carl1961/WirelessWeatherReWork/Pictures/20250413_174417.jpg

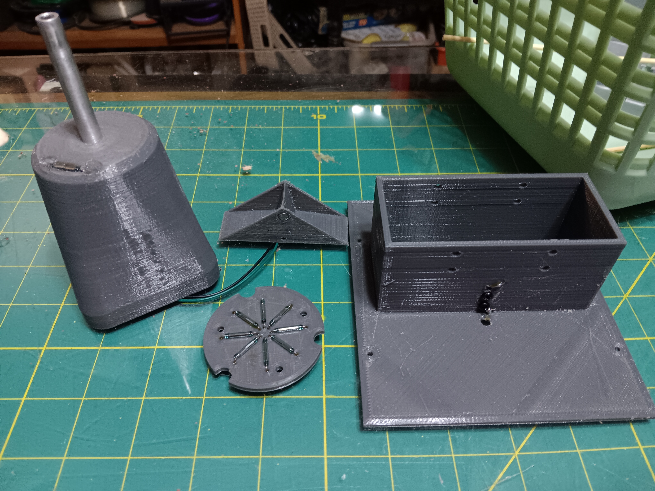
Pictures/20250413_174417.jpg
