carl1961/WirelessWeatherReWork/Pictures/20250413_174422.jpg

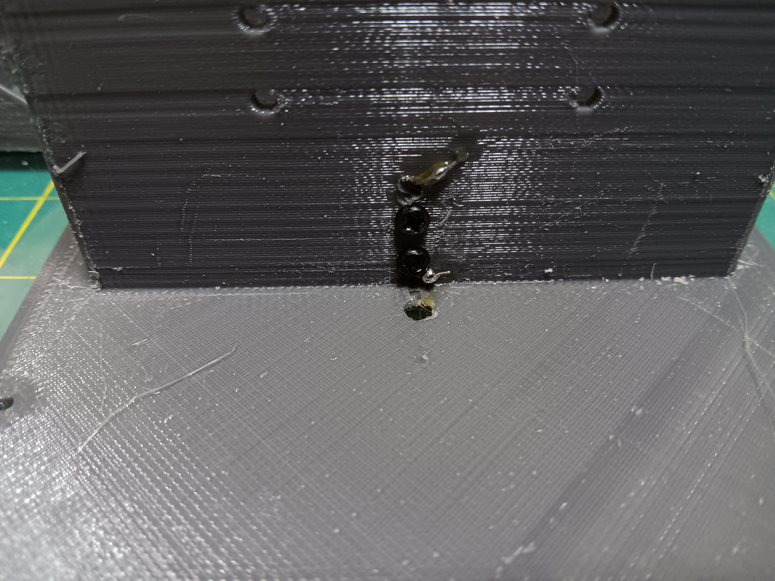
Pictures/20250413_174422.jpg
