carl1961/WirelessWeatherReWork/Pictures/20250413_174429.jpg

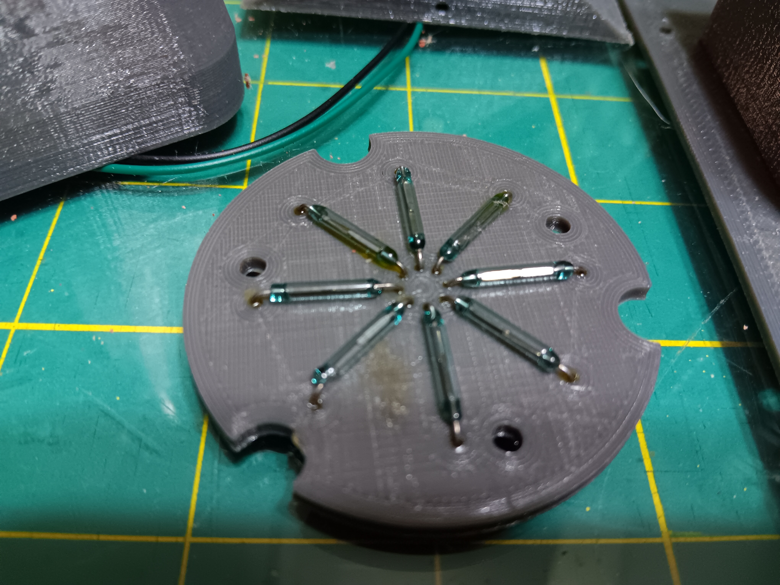
Pictures/20250413_174429.jpg
