carl1961/WirelessWeatherReWork/Pictures/20250413_174439.jpg

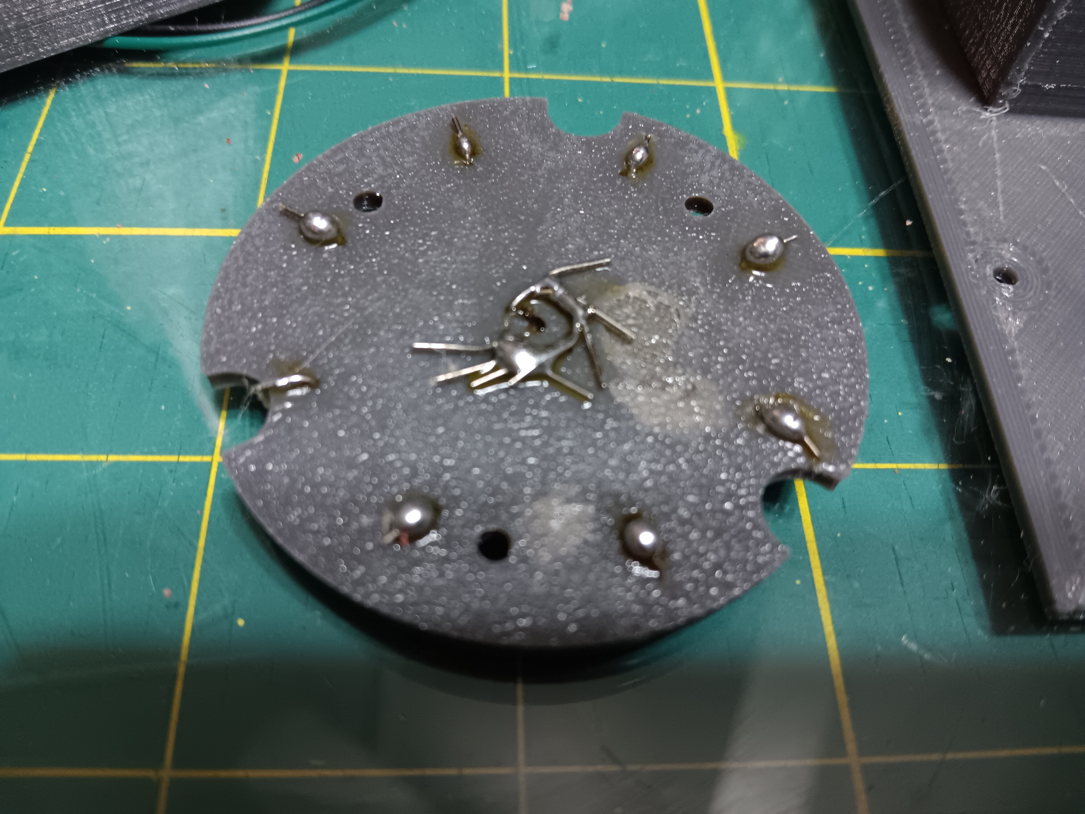
Pictures/20250413_174439.jpg
