carl1961/WirelessWeatherReWork/Pictures/20250413_174446.jpg

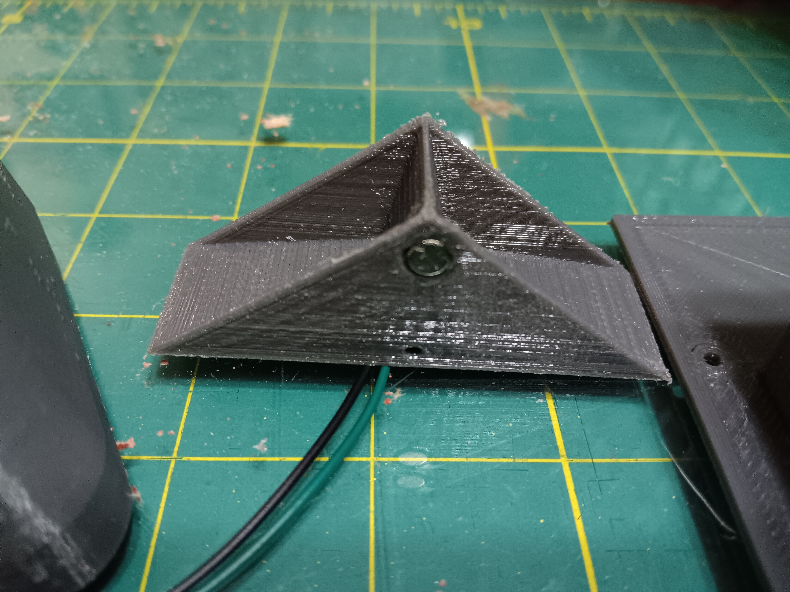
Pictures/20250413_174446.jpg
