carl1961/WirelessWeatherReWork/Pictures/20250413_174532.jpg

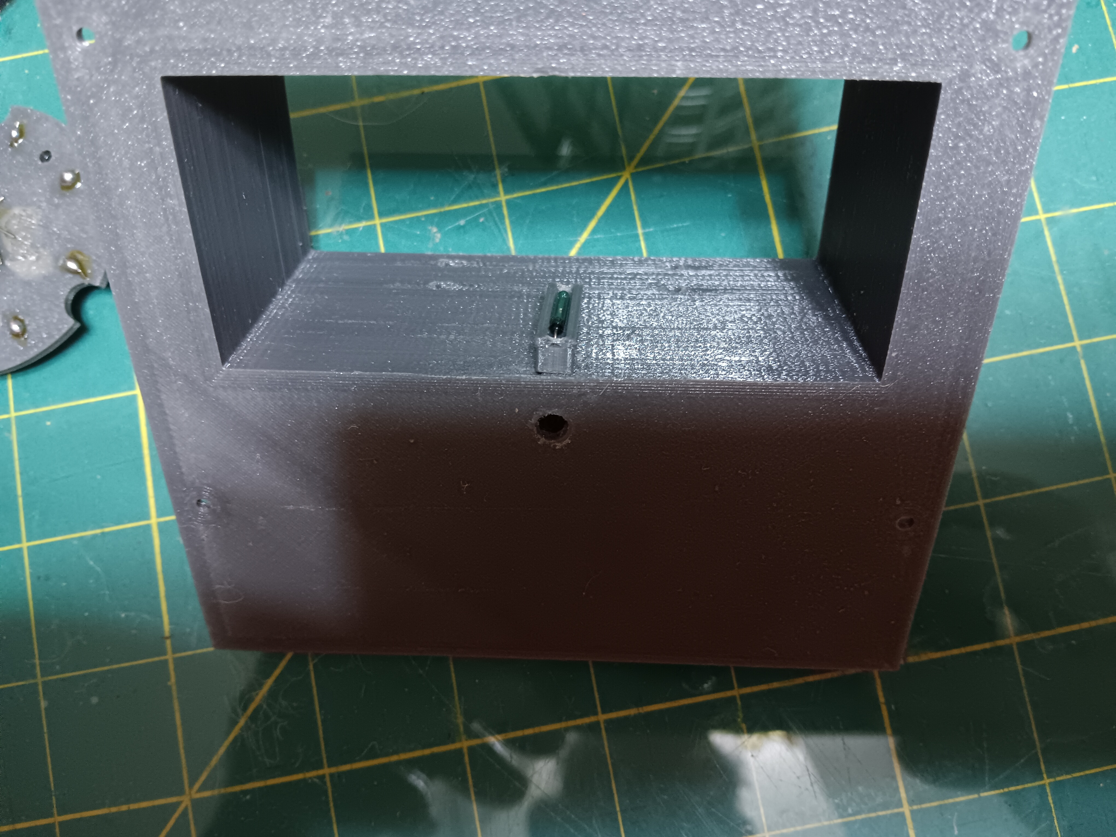
Pictures/20250413_174532.jpg
