carl1961/WirelessWeatherReWork/Pictures/20250414_012039.jpg

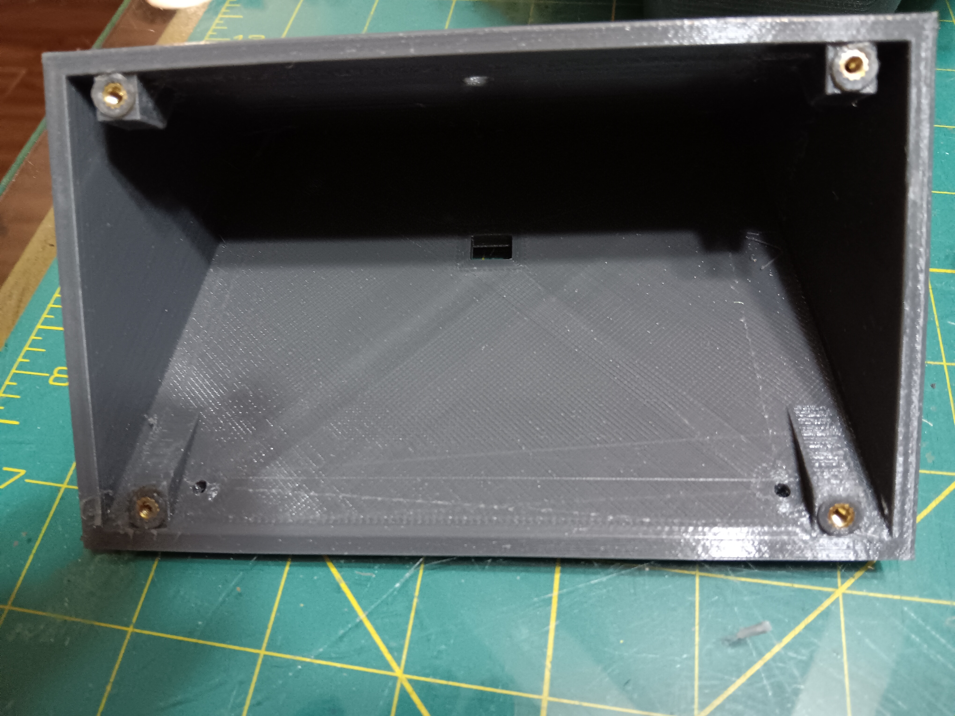
Pictures/20250414_012039.jpg
