carl1961/WirelessWeatherReWork/Pictures/20250414_012103.jpg

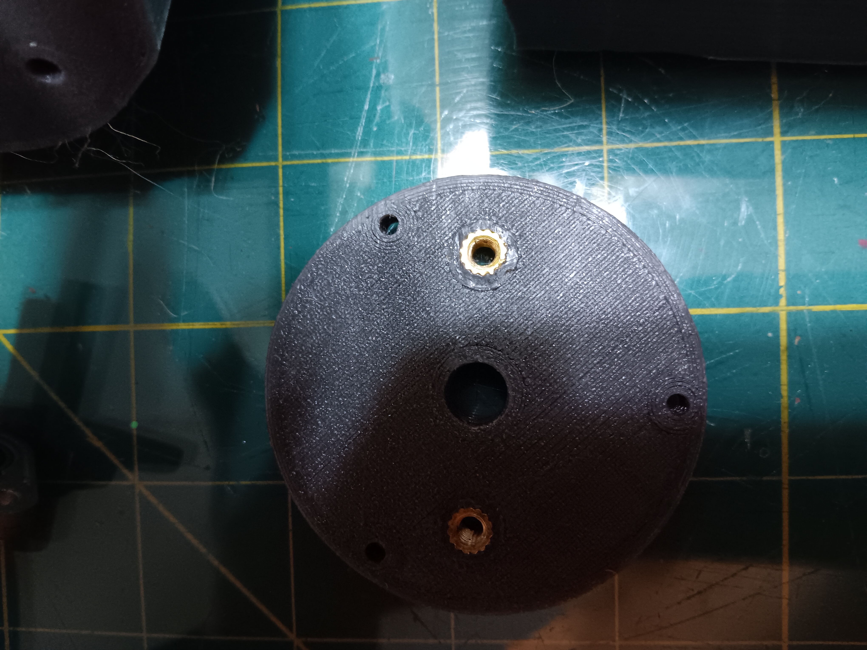
Pictures/20250414_012103.jpg
