carl1961/WirelessWeatherReWork/Pictures/20250414_012409.jpg

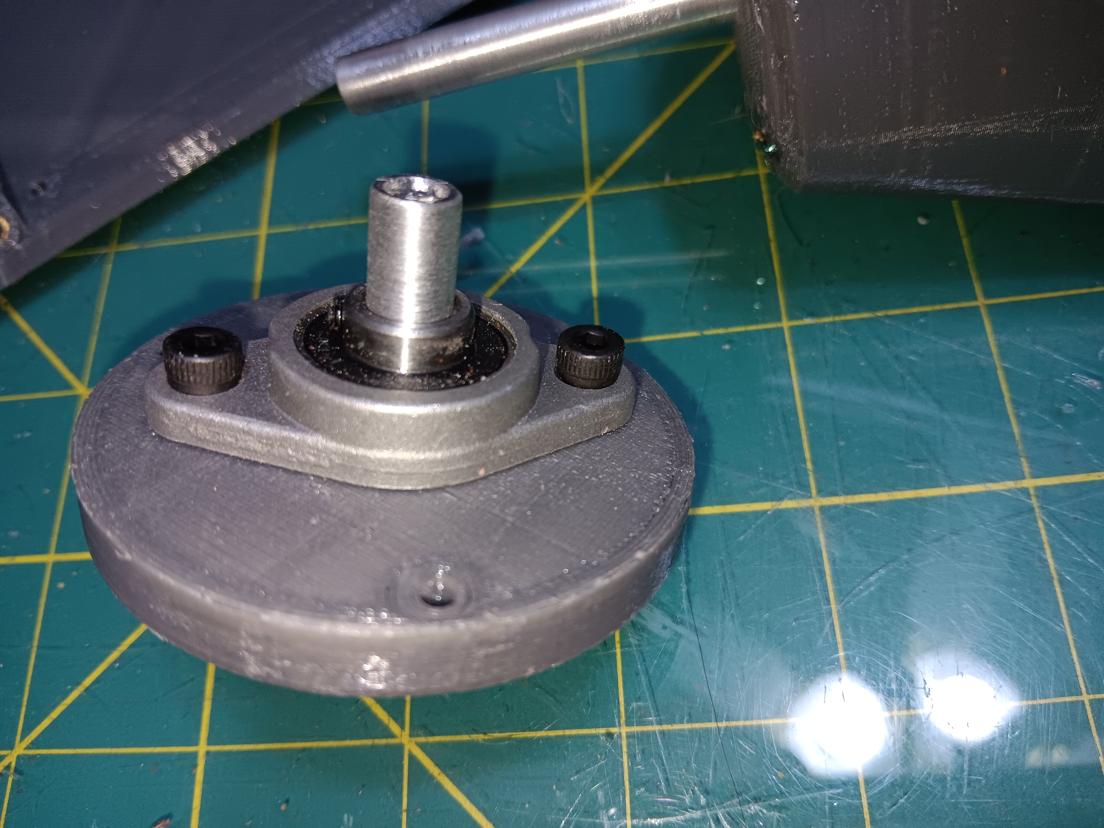
Pictures/20250414_012409.jpg
