carl1961/WirelessWeatherReWork/Pictures/20250414_012421.jpg

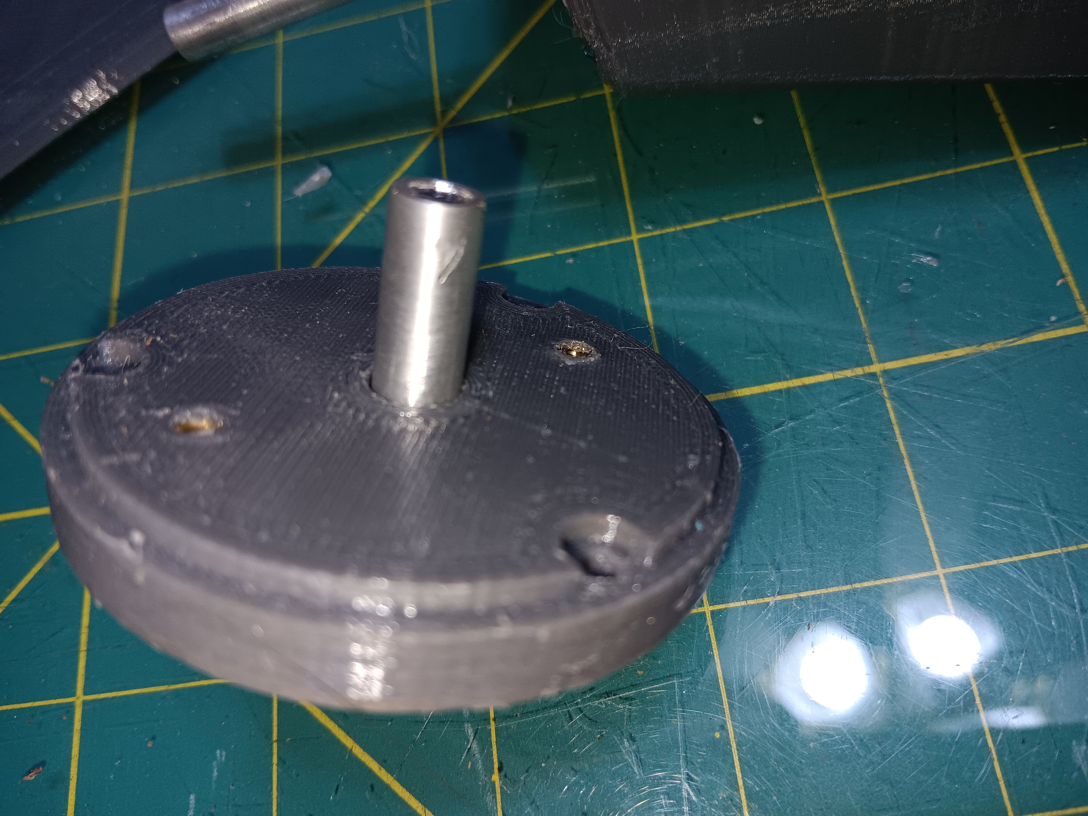
Pictures/20250414_012421.jpg
