carl1961/WirelessWeatherReWork/Pictures/20250416_141832.jpg

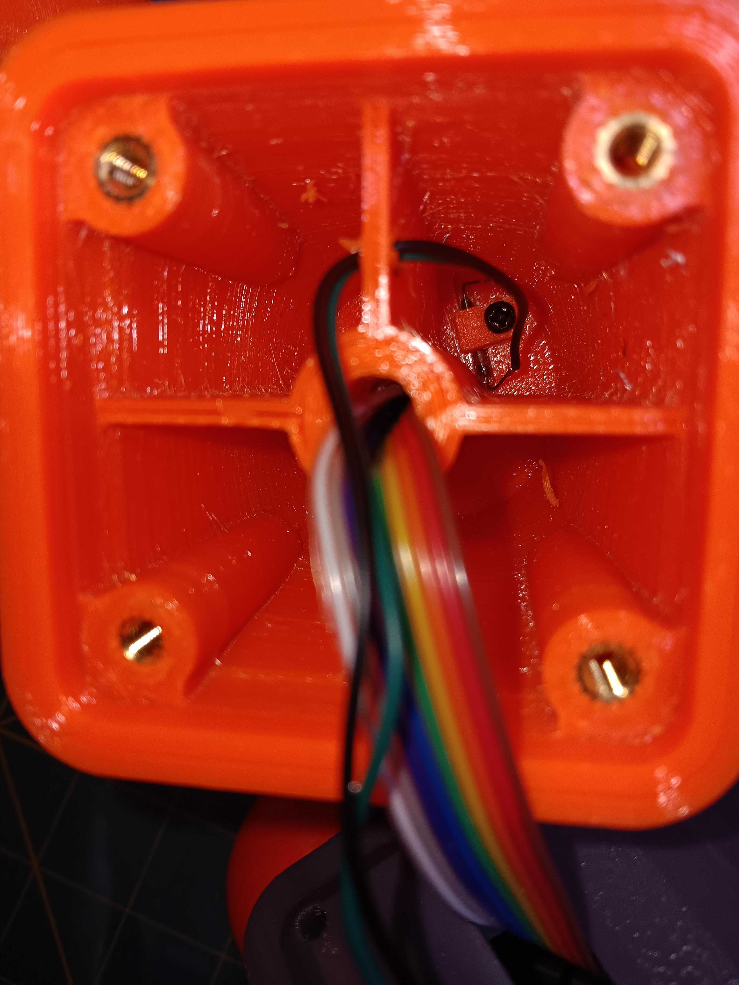
Pictures/20250416_141832.jpg
