carl1961/WirelessWeatherReWork/Pictures/20250417_025317.jpg

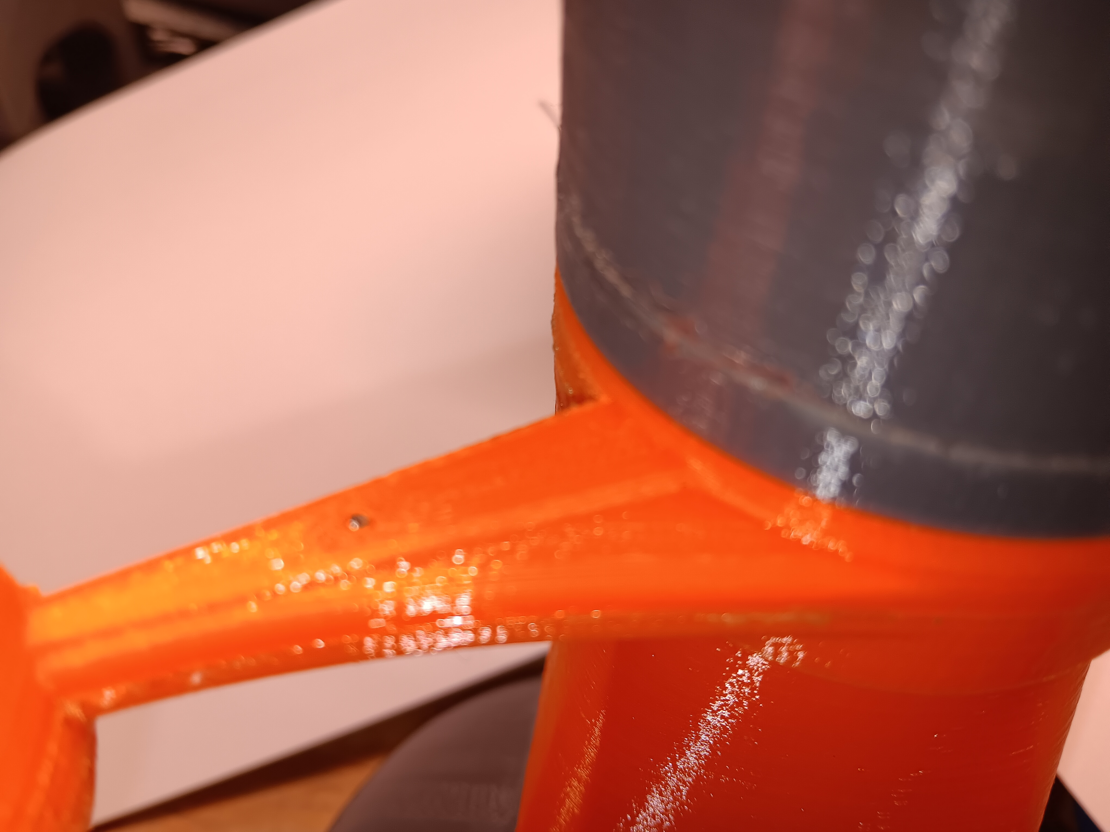
Pictures/20250417_025317.jpg
