carl1961/WirelessWeatherReWork/Pictures/20250417_025332.jpg

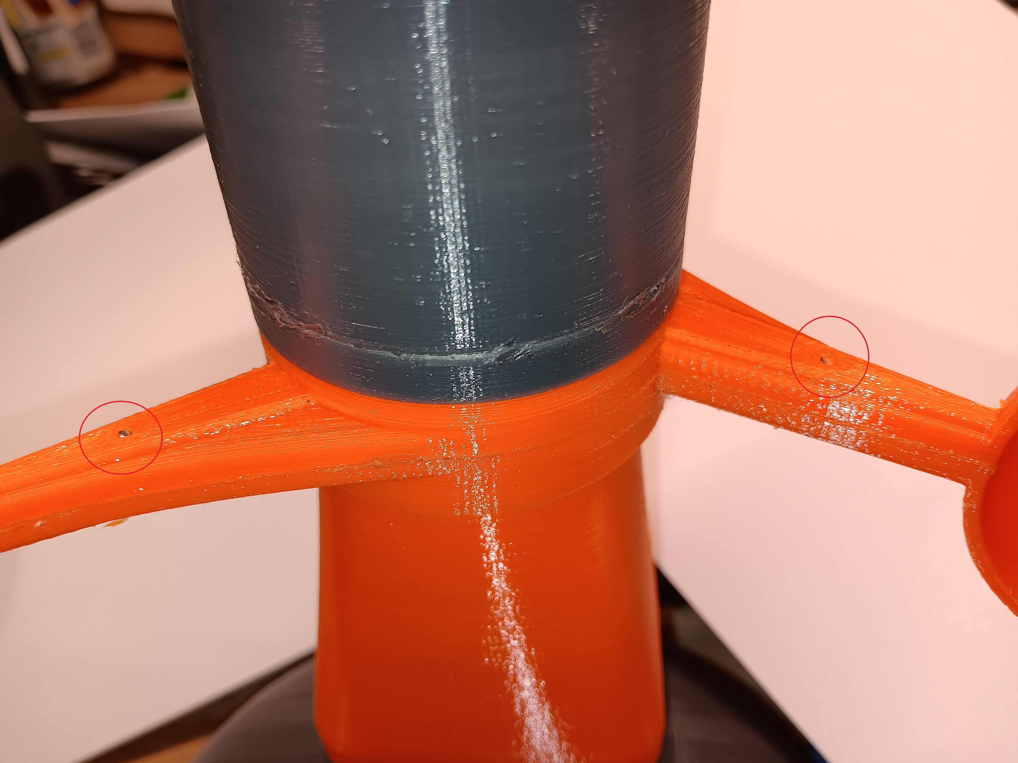
Pictures/20250417_025332.jpg
