carl1961/WirelessWeatherReWork/Pictures/WIN_20250417_22_18_12_Pro.jpg

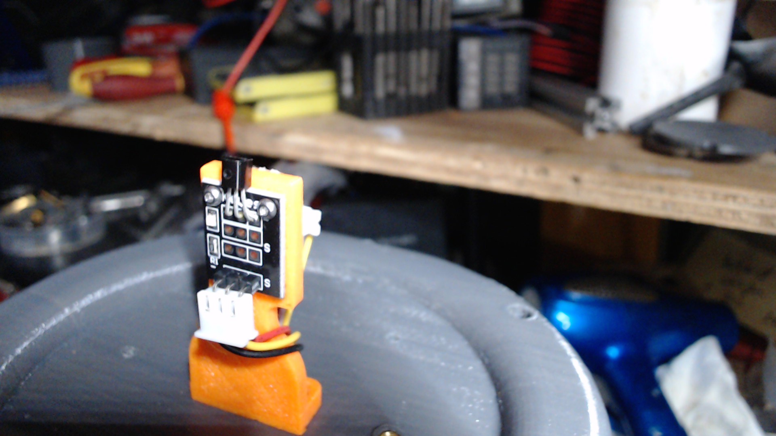
Pictures/WIN_20250417_22_18_12_Pro.jpg
