carl1961/WirelessWeatherReWork/Pictures/WIN_20250417_22_18_52_Pro.jpg

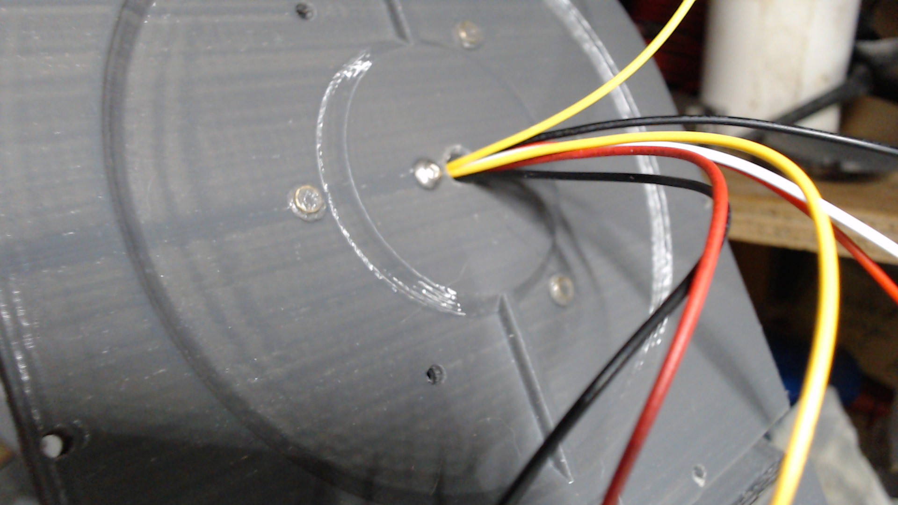
Pictures/WIN_20250417_22_18_52_Pro.jpg
