carl1961/WirelessWeatherReWork/Pictures/WIN_20250417_22_20_46_Pro.jpg

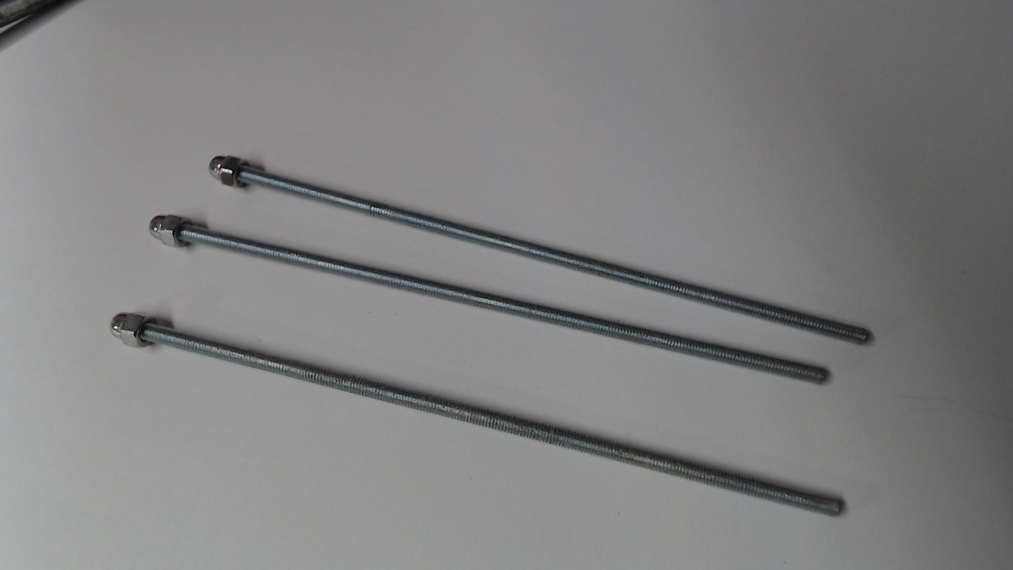
Pictures/WIN_20250417_22_20_46_Pro.jpg
