carl1961/WirelessWeatherReWork/STL/Screenshot 2025-04-13 030711.jpg

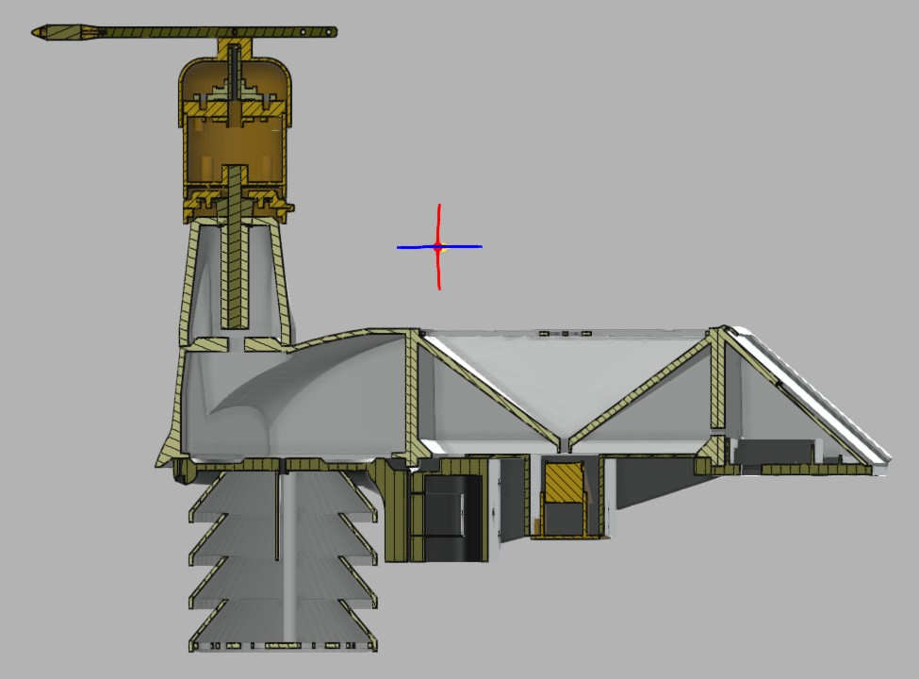
STL/Screenshot 2025-04-13 030711.jpg
