carl1961/WirelessWeatherReWork/STL/Reed-Mount-V2.stl

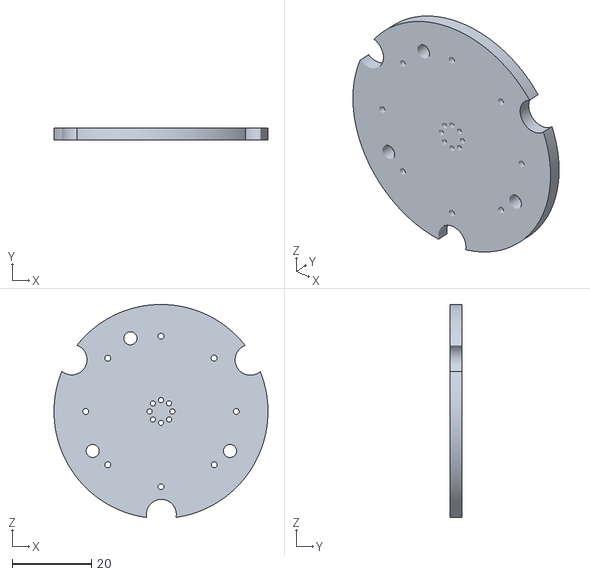
[picture p43: CAD file, 2025-04-13]
STL/Reed-Mount-V2.stl
54.0 x 3.00 x 53.8
