carl1961/WirelessWeatherReWork/STL/Solar-Modul-125-195-2.stl

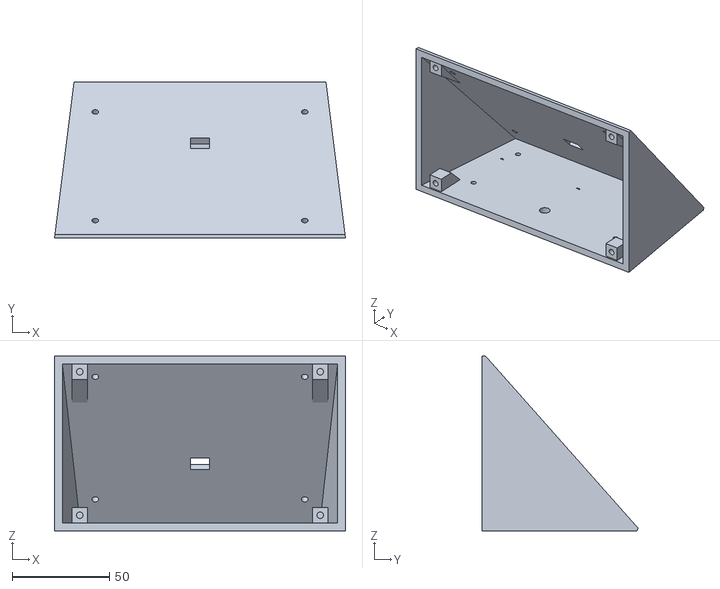
[picture p44: CAD file, 2025-04-13]
STL/Solar-Modul-125-195-2.stl
150.0 x 80.6 x 90.0
