carl1961/WirelessWeatherReWork/Pictures/20250414_012158.jpg

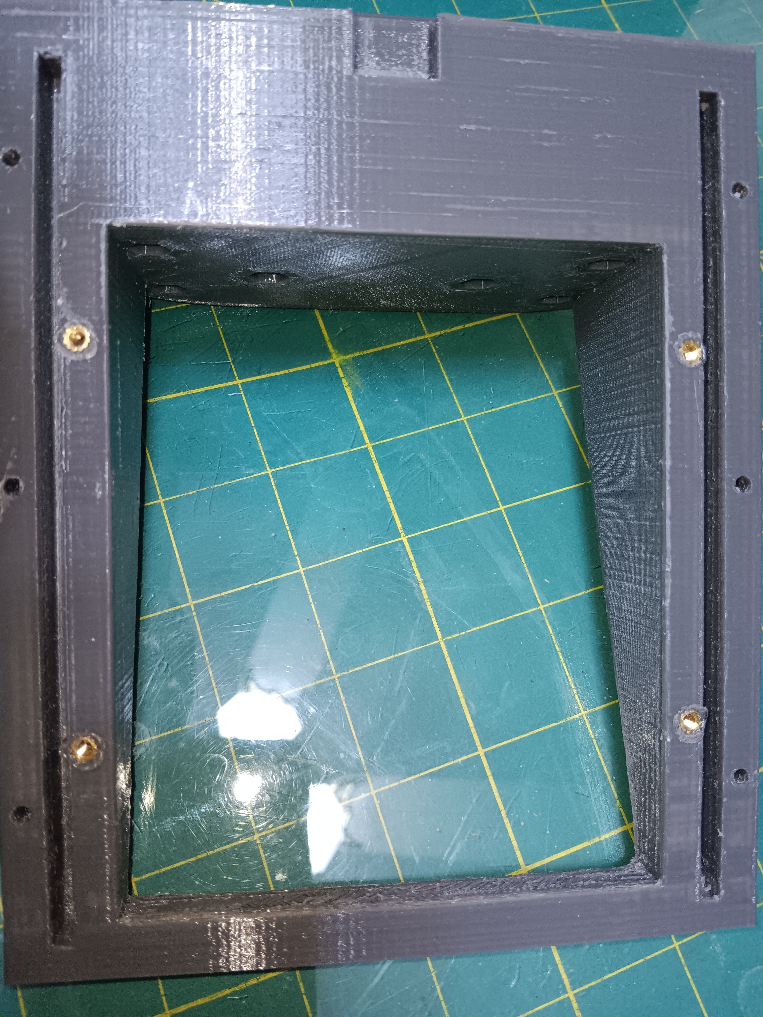
Pictures/20250414_012158.jpg
