carl1961/WirelessWeatherReWork/Pictures/20250416_141912.jpg

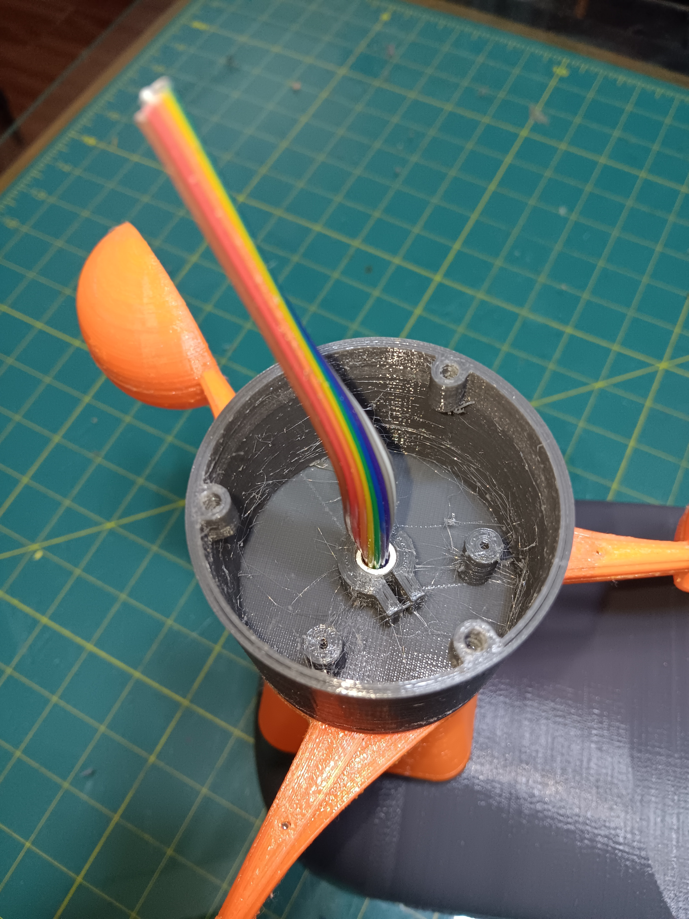
Pictures/20250416_141912.jpg
